RWTH-EBC/OSIGBApp/Firmware/components/GW/src/TMP_MAX31865.c

#include "TMP_MAX31865.h"
#include <esp_log.h>
#include <string.h>
#include <math.h>

#define CLOCK_SPEED_HZ (1000000) // 1 MHz

static const char *TAG = "MAX31865";
static max31865_t dev;
static max31865_t dev2;

/*************************************
                SPI
 *************************************/

static esp_err_t writeRegister(u_int8_t devnum, uint8_t addr, uint8_t bytes, uint8_t *data)
{
	spi_transaction_t t;
	memset(&t, 0, sizeof(t));
	t.flags = SPI_TRANS_USE_TXDATA;
	t.addr = (addr | 0x80);
	t.length = bytes * 8;
	for (uint8_t i = 0; i < bytes; i++)
		t.tx_data[i] = data[i];
	
	ESP_LOGD(TAG, "Write $0x%02x = 0x%02x", (uint8_t)t.addr, data[0]);
	switch (devnum)
	{
	case 1:
		return spi_device_transmit(dev.spi_dev, &t);
		break;
	case 2:
		return spi_device_transmit(dev2.spi_dev, &t);
	
	default:
		return ESP_OK;
		break;
	}
	
}
static esp_err_t readRegister(u_int8_t devnum, uint8_t addr, uint8_t bytes, uint8_t *data)
{	
	esp_err_t err = ESP_OK;
	spi_transaction_t t;
	memset(&t, 0, sizeof(t));
	t.flags = SPI_TRANS_USE_TXDATA;
	t.addr = (addr &= 0x7F); // make sure top bit is not set
	t.length = bytes * 8;
	t.rx_buffer = data;
	for (uint8_t i = 0; i < bytes; i++)
		t.tx_data[i] = 0xFF;

	switch (devnum)
	{
		case 1:
			err = spi_device_transmit(dev.spi_dev, &t);
			break;
		case 2:
			err = spi_device_transmit(dev2.spi_dev, &t);

		default:
			break;
	}
	if (bytes == 1)
		ESP_LOGD(TAG, "Read $%02x = 0x%02x", (uint8_t)t.addr, data[0]);
	else
		ESP_LOGD(TAG, "Read $%02x = 0x%02x 0x%02x", (uint8_t)t.addr, data[0], data[1]);

	return err;
}

/*************************************
                MAX31865
 *************************************/
/* 
static uint8_t readFault(u_int8_t devnum)
{
	ESP_LOGI(TAG, "Read Fault");
	uint8_t code = 0;
	readRegister(devnum, MAX31856_FAULTSTAT_REG, 1, &code);
	return code;
}
 */
static void clearFault(u_int8_t devnum)
{
	ESP_LOGI(TAG, "Clear Fault");
	uint8_t code = 0;
	readRegister(devnum, MAX31856_CONFIG_REG, 1, &code);
	code &= ~0x2C;
	code |= MAX31856_CONFIG_FAULTSTAT;
	writeRegister(devnum, MAX31856_CONFIG_REG, 1, &code);
}

static void autoConvert(u_int8_t devnum, bool status)
{
	ESP_LOGI(TAG, "%s auto-conversion", status ? "Enable" : "Disable");

	uint8_t code = 0;
	readRegister(devnum, MAX31856_CONFIG_REG, 1, &code);

	if (status)
		code |= MAX31856_CONFIG_MODEAUTO; // enable autoconvert
	else
		code &= ~MAX31856_CONFIG_MODEAUTO; // disable autoconvert

	writeRegister(devnum, MAX31856_CONFIG_REG, 1, &code);
}

static void setWires(u_int8_t devnum, max31865_numwires_t wires)
{
	ESP_LOGI(TAG, "Set %d wires", dev.wires + 2);

	uint8_t code = 0;
	readRegister(devnum, MAX31856_CONFIG_REG, 1, &code);

	if (wires == MAX31865_3WIRE)
		code |= MAX31856_CONFIG_3WIRE; // 3 wires
	else
		code &= ~MAX31856_CONFIG_3WIRE; // 2 or 4 wire

	writeRegister(devnum, MAX31856_CONFIG_REG, 1, &code);
}

static void setNotch(u_int8_t devnum, max31865_notch_t notch)
{
	ESP_LOGI(TAG, "Set notch at %d Hz", (notch == MAX31865_50Hz ? 50 : 60));

	uint8_t code = 0;
	readRegister(devnum, MAX31856_CONFIG_REG, 1, &code);

	if (notch == MAX31865_50Hz)
		code |= MAX31856_CONFIG_FILT50HZ; // 50 Hz
	else
		code &= ~MAX31856_CONFIG_FILT50HZ; // 60 Hz

	writeRegister(devnum, MAX31856_CONFIG_REG, 1, &code);
}

static void oneShot(u_int8_t devnum, bool status)
{
	ESP_LOGI(TAG, "%s 1-shot mode", status ? "Enable" : "Disable");

	uint8_t code = 0;
	readRegister(devnum, MAX31856_CONFIG_REG, 1, &code);

	if (status)
		code |= MAX31856_CONFIG_1SHOT; // 1-shot
	else
		code &= ~MAX31856_CONFIG_1SHOT; // Auto-conversion

	writeRegister(devnum, MAX31856_CONFIG_REG, 1, &code);
}

static uint16_t readRTD(u_int8_t devnum)
{
	// gpio_set_level(2, 1);
	// vTaskDelay(5000 / portTICK_PERIOD_MS);
	uint16_t rtd;
//	for (size_t i = 0; i < 2; i++)
//	{
	clearFault(devnum);
	vTaskDelay(1 / portTICK_PERIOD_MS);

	oneShot(devnum, true);
	//vTaskDelay(1 / portTICK_PERIOD_MS);

	uint8_t buffer[2] = {0, 0};
	readRegister(devnum, MAX31856_RTDMSB_REG, 2, buffer);

	rtd = (buffer[0] << 8) | buffer[1];
	rtd >>= 1; // remove fault

	//}
	// gpio_set_level(2, 0);

	return rtd;
}

static void max_spi_pre_transfer_callback(void)
{
    gpio_set_level(PIN_MAX_CS_1, 0);
}

static void max_spi_post_transfer_callback(void)
{
	gpio_set_level(PIN_MAX_CS_1, 1);    
}

static void max_spi_pre_transfer_callback2(void)
{
    gpio_set_level(PIN_MAX_CS_2, 0);
}

static void max_spi_post_transfer_callback2(void)
{
	gpio_set_level(PIN_MAX_CS_2, 1);    
}

void max31865_enable(u_int8_t devnum, bool status)
{
	ESP_LOGI(TAG, "%s bias", status ? "Enable" : "Disable");

	uint8_t code = 0;
	readRegister(devnum, MAX31856_CONFIG_REG, 1, &code);

	if (status)
		code |= MAX31856_CONFIG_BIAS; // enable bias
	else
		code &= ~MAX31856_CONFIG_BIAS; // disable bias

	writeRegister(devnum, MAX31856_CONFIG_REG, 1, &code);
}

esp_err_t init_MAX31865_1(float _RTD_nominal, float _REF_resistor, max31865_numwires_t _wires)
{
	ESP_LOGI(TAG, "Init MAX31865 module");

	gpio_set_direction(PIN_MAX_CS_1, GPIO_MODE_OUTPUT);
	gpio_set_level(PIN_MAX_CS_1, 1);
	memset(&dev, 0, sizeof(dev));

	gpio_set_direction(PIN_MAX_CS_2, GPIO_MODE_OUTPUT);
	gpio_set_level(PIN_MAX_CS_2, 1);
	memset(&dev2, 0, sizeof(dev2));


	
	// Configure SPI bus
	spi_bus_config_t bus_cfg = {
		.miso_io_num = PIN_MAX_MISO,
		.mosi_io_num = PIN_MAX_MOSI,
		.sclk_io_num = PIN_MAX_SCK,
		.quadwp_io_num = -1,
		.quadhd_io_num = -1};

	ESP_LOGI(TAG, "Configuring SPI bus");
	ESP_ERROR_CHECK(spi_bus_initialize(VSPI_HOST, &bus_cfg, 0));

	// Configure device 1
	dev.RTD_nominal = _RTD_nominal;
	dev.REF_resistor = _REF_resistor;
	dev.wires = _wires;
	dev.spi_cfg.clock_speed_hz = 1 * 1000 * 1000;	// Clock out at 1 MHz
	dev.spi_cfg.address_bits = 8;
	dev.spi_cfg.command_bits = 0;
	dev.spi_cfg.mode = 1;				   			// SPI mode 1
	dev.spi_cfg.spics_io_num = -1;					// PIN_MAX_CS_1; Embedded CS control fails, using pre/post-transfer function to drive CS
	dev.spi_cfg.queue_size = 1;
	dev.spi_cfg.pre_cb  = (transaction_cb_t)max_spi_pre_transfer_callback;
	dev.spi_cfg.post_cb = (transaction_cb_t)max_spi_post_transfer_callback;

	ESP_LOGI(TAG, "Configuring SPI device descriptor");
	ESP_ERROR_CHECK(spi_bus_add_device(VSPI_HOST, &dev.spi_cfg, &dev.spi_dev));

	max31865_enable(1, false);		// Disable bias
	setWires(1, dev.wires);	 	// Set number of RTD wires
	clearFault(1);			 	// Clear fault status
	autoConvert(1, false);		 	// Disable auto conversion
	setNotch(1, MAX31865_50Hz); 	// Set 50 Hz notch filter
	vTaskDelay(10 / portTICK_PERIOD_MS);
	// gpio_set_level(PIN_MAX_CS_1, 0);
	return ESP_OK;
}

esp_err_t init_MAX31865_2(float _RTD_nominal, float _REF_resistor, max31865_numwires_t _wires)
{
	ESP_LOGI(TAG, "Init MAX31865 module 2");

	gpio_set_direction(PIN_MAX_CS_2, GPIO_MODE_OUTPUT);
	gpio_set_level(PIN_MAX_CS_2, 1);
	memset(&dev2, 0, sizeof(dev2));

	// Configure device 2
	dev2.RTD_nominal = _RTD_nominal;
	dev2.REF_resistor = _REF_resistor;
	dev2.wires = _wires;
	dev2.spi_cfg.clock_speed_hz = 1 * 1000 * 1000;	// Clock out at 1 MHz
	dev2.spi_cfg.address_bits = 8;
	dev2.spi_cfg.command_bits = 0;
	dev2.spi_cfg.mode = 1;				   			// SPI mode 1
	dev2.spi_cfg.spics_io_num = -1;					// PIN_MAX_CS_1; Embedded CS control fails, using pre/post-transfer function to drive CS
	dev2.spi_cfg.queue_size = 1;
	dev2.spi_cfg.pre_cb  = (transaction_cb_t)max_spi_pre_transfer_callback2;
	dev2.spi_cfg.post_cb = (transaction_cb_t)max_spi_post_transfer_callback2;

	ESP_LOGI(TAG, "Configuring SPI device descriptor");
	ESP_ERROR_CHECK(spi_bus_add_device(VSPI_HOST, &dev2.spi_cfg, &dev2.spi_dev));

	max31865_enable(2, false);		// Disable bias
	setWires(2, dev2.wires);	 	// Set number of RTD wires
	clearFault(2);			 	// Clear fault status
	autoConvert(2, false);		 	// Disable auto conversion
	setNotch(2, MAX31865_50Hz); 	// Set 50 Hz notch filter
	vTaskDelay(10 / portTICK_PERIOD_MS);
	// gpio_set_level(PIN_MAX_CS_2, 0);
	return ESP_OK;
}




esp_err_t free_MAX31865()
{
	return spi_bus_remove_device(dev.spi_dev);
}

float max31865_temperature_1()
{

	// gpio_set_level(2, 1);
	// http://www.analog.com/media/en/technical-documentation/application-notes/AN709_0.pdf

	float Z1, Z2, Z3, Z4, Rt, temp;

	Rt = readRTD(1);
	Rt /= 32768.0;
	Rt *= dev.REF_resistor;

	// Serial.print("\nResistance: "); Serial.println(Rt, 8);

	Z1 = -RTD_A;
	Z2 = RTD_A * RTD_A - (4 * RTD_B);
	Z3 = (4 * RTD_B) / dev.RTD_nominal;
	Z4 = 2 * RTD_B;

	temp = Z2 + (Z3 * Rt);
	temp = (sqrt(temp) + Z1) / Z4;

	if (temp >= 0)
		return temp;

	
	Rt /= dev.RTD_nominal;
	Rt *= 100; // normalize to 100 ohm

	float rpoly = Rt;

	temp = -242.02;
	temp += 2.2228 * rpoly;
	rpoly *= Rt; // square
	temp += 2.5859e-3 * rpoly;
	rpoly *= Rt; // ^3
	temp -= 4.8260e-6 * rpoly;
	rpoly *= Rt; // ^4
	temp -= 2.8183e-8 * rpoly;
	rpoly *= Rt; // ^5
	temp += 1.5243e-10 * rpoly;

	// gpio_set_level(2, 0);

	return temp;
}

float max31865_temperature_2()
{
	// http://www.analog.com/media/en/technical-documentation/application-notes/AN709_0.pdf
	// gpio_set_level(2, 1);
	float Z1, Z2, Z3, Z4, Rt, temp;

	Rt = readRTD(2);
	Rt /= 32768.0;
	Rt *= dev.REF_resistor;

	// Serial.print("\nResistance: "); Serial.println(Rt, 8);

	Z1 = -RTD_A;
	Z2 = RTD_A * RTD_A - (4 * RTD_B);
	Z3 = (4 * RTD_B) / dev.RTD_nominal;
	Z4 = 2 * RTD_B;

	temp = Z2 + (Z3 * Rt);
	temp = (sqrt(temp) + Z1) / Z4;

	if (temp >= 0)
		return temp;

	
	Rt /= dev.RTD_nominal;
	Rt *= 100; // normalize to 100 ohm

	float rpoly = Rt;

	temp = -242.02;
	temp += 2.2228 * rpoly;
	rpoly *= Rt; // square
	temp += 2.5859e-3 * rpoly;
	rpoly *= Rt; // ^3
	temp -= 4.8260e-6 * rpoly;
	rpoly *= Rt; // ^4
	temp -= 2.8183e-8 * rpoly;
	rpoly *= Rt; // ^5
	temp += 1.5243e-10 * rpoly;


	// gpio_set_level(2, 0);
	return temp;
}
